CircuitMonkey/eight-bit-computer-m1/modules/alu/m1-alu.brd

## EAGLE design modules/alu/m1-alu.brd (2020-04-13)

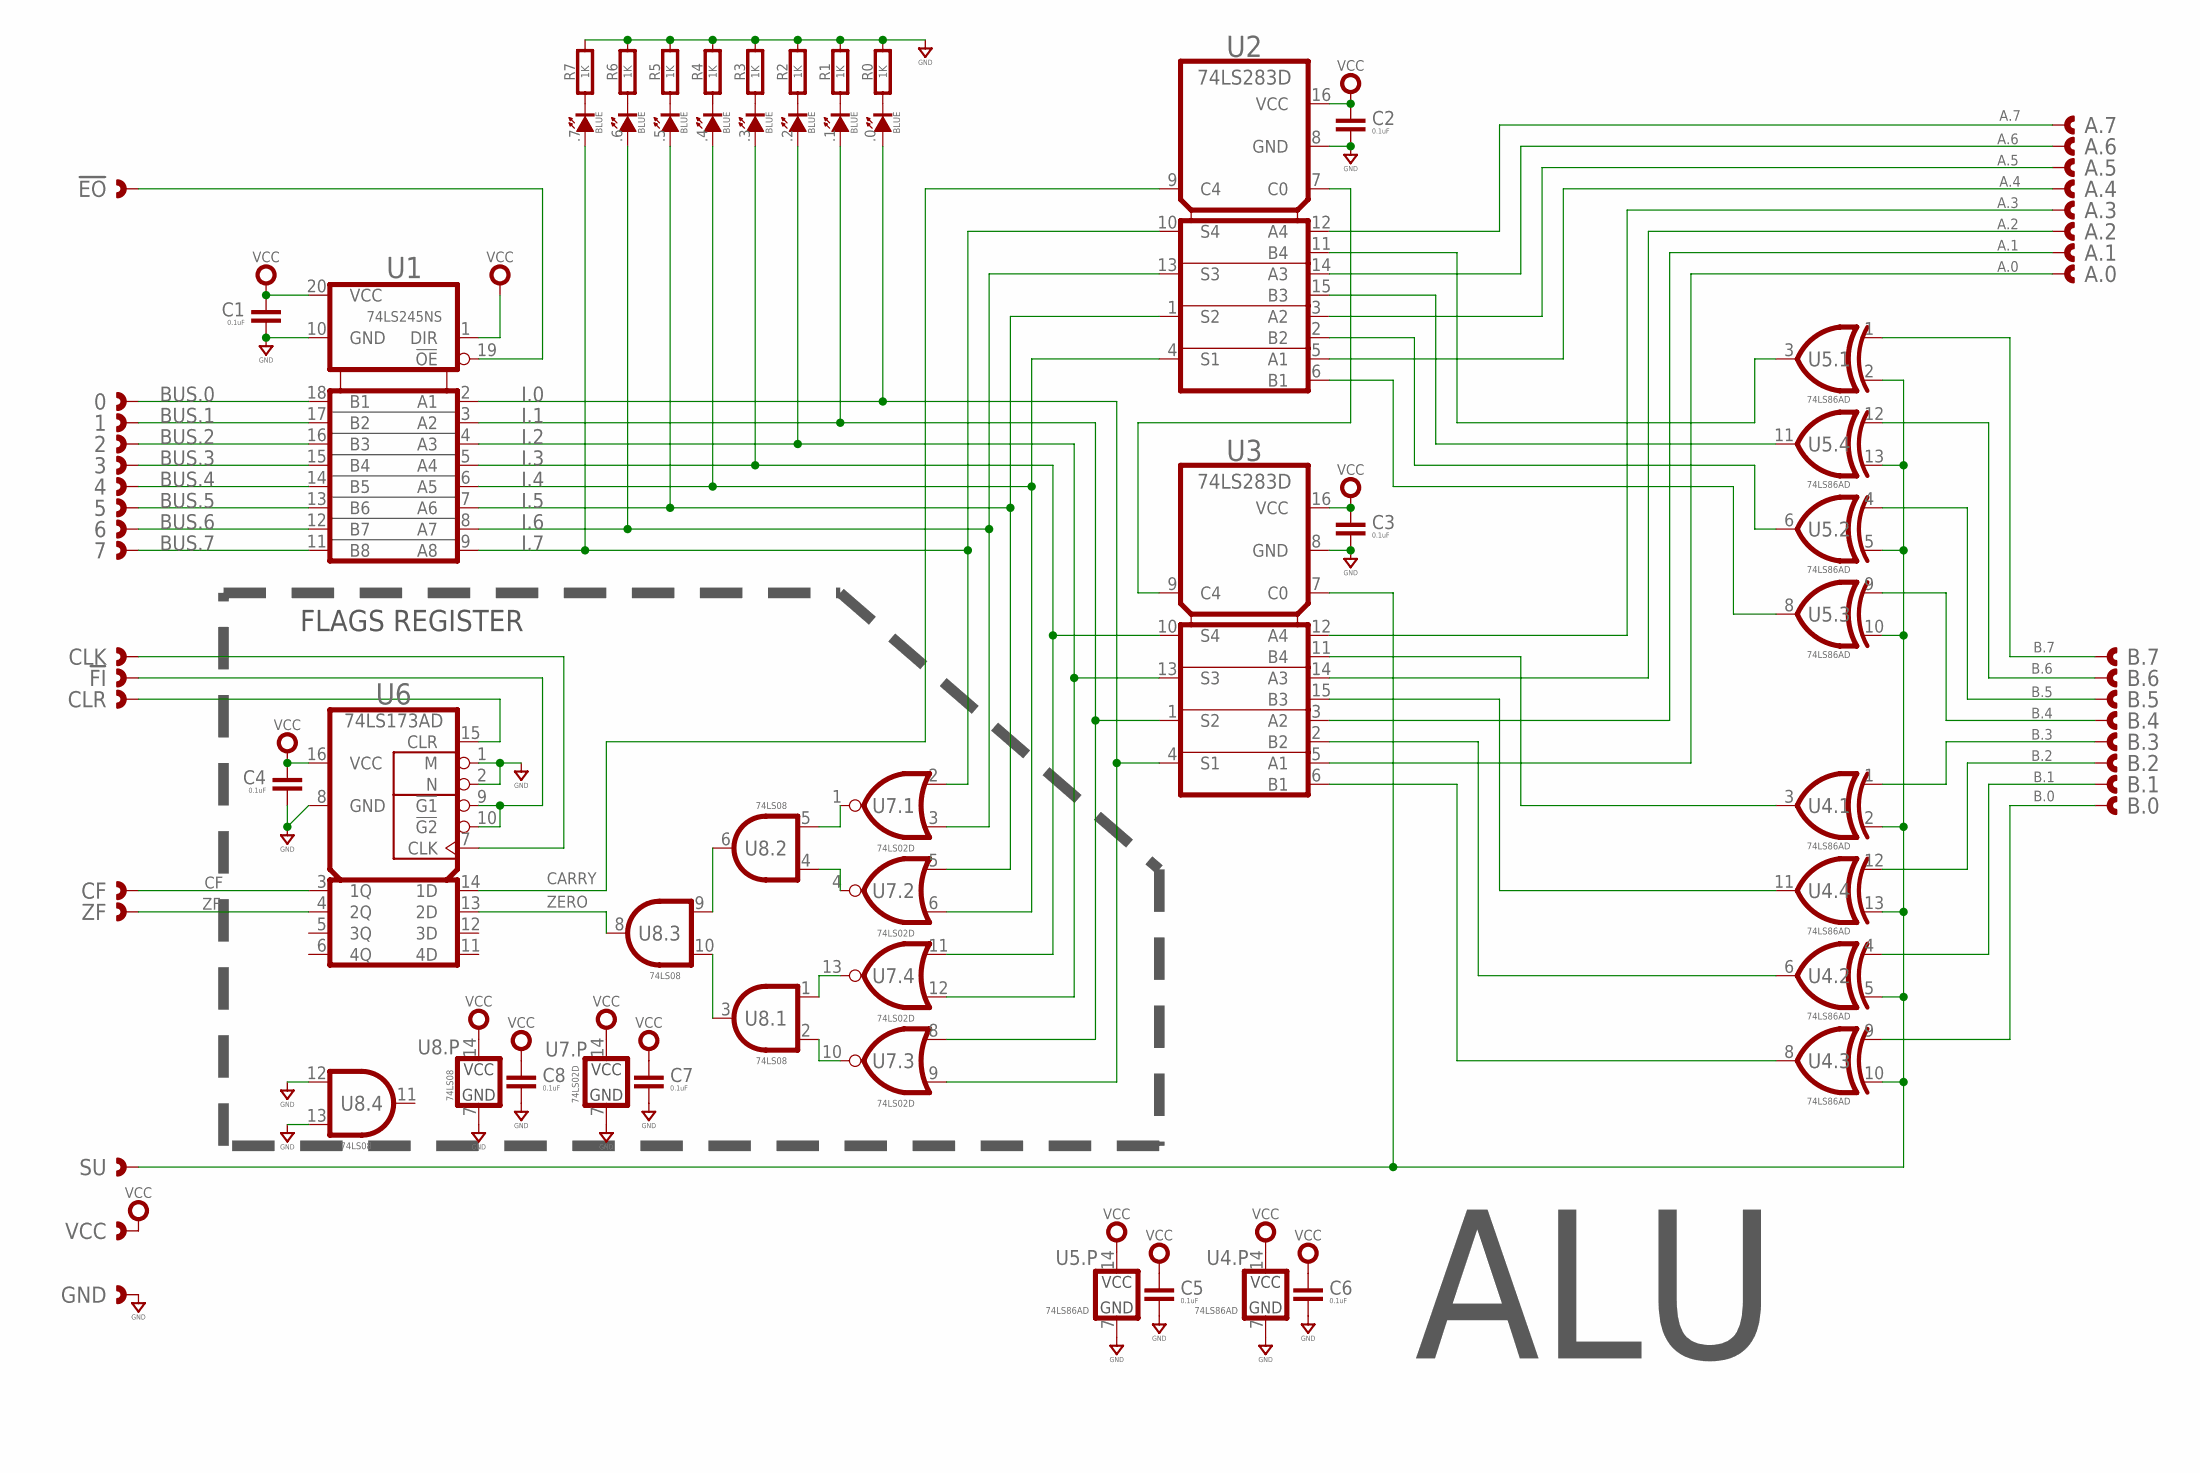
[picture p24: schematic m1-alu.sch]

Parts:
0, 1, 2, 3, 4, 5, 6, 7: CAST-01X1; CAST01-2.54MM
!EO: CAST-01X1; CAST01-2.54MM
!FI: CAST-01X1; CAST01-2.54MM
.0, .1, .2, .3, .4, .5, .6, .7: BLUE; SMD_0603
A.0, A.1, A.2, A.3, A.4, A.5, A.6, A.7: CAST-01X1; CAST01-2.54MM
B.0, B.1, B.2, B.3, B.4, B.5, B.6, B.7: CAST-01X1; CAST01-2.54MM
C1, C2, C3, C4, C5, C6, C7, C8: 0.1uF; 0603-CAP
CF: CAST-01X1; CAST01-2.54MM
CLK: CAST-01X1; CAST01-2.54MM
CLR: CAST-01X1; CAST01-2.54MM
GND: CAST-01X1; CAST01-2.54MM
R0, R1, R2, R3, R4, R5, R6, R7: 1K; 0603-RES
SU: CAST-01X1; CAST01-2.54MM
U1: 74LS245NS; SO20
U2, U3: 74LS283D; SO16
U4, U5: 74LS86AD; SOP14
U6: 74LS173AD; SO16
U7: 74LS02D; SOP14
U8: 74LS08; SOP14
VCC: CAST-01X1; CAST01-2.54MM
ZF: CAST-01X1; CAST01-2.54MM

Connections:
A.0: A.0.1, U3.5 (A1)
A.1: A.1.1, U3.3 (A2)
A.2: A.2.1, U3.14 (A3)
A.3: A.3.1, U3.12 (A4)
A.4: A.4.1, U2.5 (A1)
A.5: A.5.1, U2.3 (A2)
A.6: A.6.1, U2.14 (A3)
A.7: A.7.1, U2.12 (A4)
B.0: B.0.1, U4.9 (A)
B.1: B.1.1, U4.4 (A)
B.2: B.2.1, U4.12 (A)
B.3: B.3.1, U4.1 (A)
B.4: B.4.1, U5.9 (A)
B.5: B.5.1, U5.4 (A)
B.6: B.6.1, U5.12 (A)
B.7: B.7.1, U5.1 (A)
BUS.0: 0.1, U1.18 (B1)
BUS.1: 1.1, U1.17 (B2)
BUS.2: 2.1, U1.16 (B3)
BUS.3: 3.1, U1.15 (B4)
BUS.4: 4.1, U1.14 (B5)
BUS.5: 5.1, U1.13 (B6)
BUS.6: 6.1, U1.12 (B7)
BUS.7: 7.1, U1.11 (B8)
CARRY: U2.9 (C4), U6.14 (1D)
CF: CF.1, U6.3 (1Q)
GND: C1.2, C2.2, C3.2, C4.2, C5.2, C6.2, C7.2, C8.2, GND.1, R0.2, R1.2, R2.2, R3.2, R4.2, R5.2, R6.2, R7.2, U1.10 (GND), U2.8 (GND), U3.8 (GND), U4.7 (GND), U5.7 (GND), U6.1 (M), U6.2 (N), U6.8 (GND), U7.7 (GND), U8.7 (GND), U8.12 (A), U8.13 (B)
I.0: .0.A, U1.2 (A1), U3.4 (S1), U7.9 (B)
I.1: .1.A, U1.3 (A2), U3.1 (S2), U7.8 (A)
I.2: .2.A, U1.4 (A3), U3.13 (S3), U7.12 (B)
I.3: .3.A, U1.5 (A4), U3.10 (S4), U7.11 (A)
I.4: .4.A, U1.6 (A5), U2.4 (S1), U7.6 (B)
I.5: .5.A, U1.7 (A6), U2.1 (S2), U7.5 (A)
I.6: .6.A, U1.8 (A7), U2.13 (S3), U7.3 (B)
I.7: .7.A, U1.9 (A8), U2.10 (S4), U7.2 (A)
unnamed: U2.7 (C0), U3.9 (C4)
unnamed: SU.1, U3.7 (C0), U4.2 (B), U4.5 (B), U4.10 (B), U4.13 (B), U5.2 (B), U5.5 (B), U5.10 (B), U5.13 (B)
unnamed: U2.11 (B4), U5.3 (Y)
unnamed: U2.15 (B3), U5.11 (Y)
unnamed: U2.2 (B2), U5.6 (Y)
unnamed: U2.6 (B1), U5.8 (Y)
unnamed: U3.6 (B1), U4.8 (Y)
unnamed: U3.2 (B2), U4.6 (Y)
unnamed: U3.15 (B3), U4.11 (Y)
unnamed: U3.11 (B4), U4.3 (Y)
unnamed: U7.1 (Y), U8.5 (B)
unnamed: U7.4 (Y), U8.4 (A)
unnamed: U8.6 (Y), U8.9 (A)
unnamed: U8.3 (Y), U8.10 (B)
unnamed: U7.13 (Y), U8.1 (A)
unnamed: U7.10 (Y), U8.2 (B)
unnamed: !EO.1, U1.19 (!OE)
unnamed: .0.K (C), R0.1
unnamed: .1.K (C), R1.1
unnamed: .2.K (C), R2.1
unnamed: .3.K (C), R3.1
unnamed: .4.K (C), R4.1
unnamed: .5.K (C), R5.1
unnamed: .6.K (C), R6.1
unnamed: .7.K (C), R7.1
unnamed: !FI.1, U6.9 (!G1), U6.10 (!G2)
unnamed: CLK.1, U6.7 (CLK)
unnamed: CLR.1, U6.15 (CLR)
VCC: C1.1, C2.1, C3.1, C4.1, C5.1, C6.1, C7.1, C8.1, U1.20 (VCC), U2.16 (VCC), U3.16 (VCC), U4.14 (VCC), U5.14 (VCC), U6.16 (VCC), U7.14 (VCC), U8.14 (VCC), VCC.1
ZERO: U6.13 (2D), U8.8 (Y)
ZF: U6.4 (2Q), ZF.1

Notes on the sheet:
ALU
FLAGS REGISTER

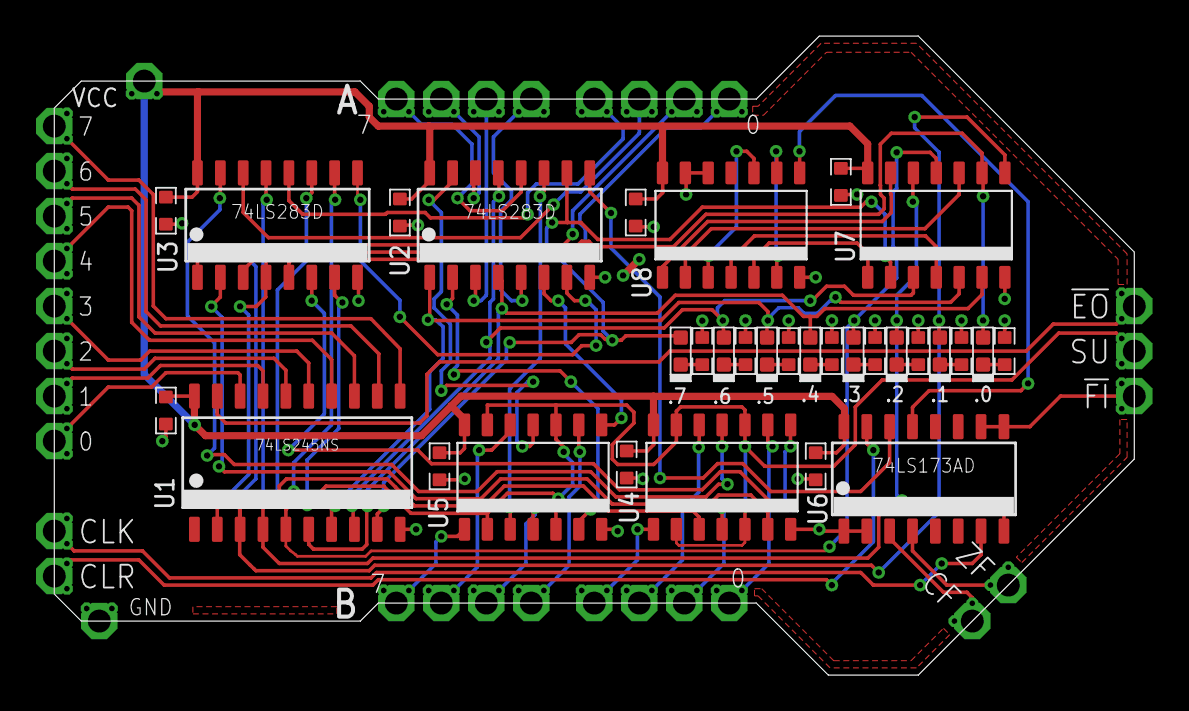
[picture p25: board m1-alu.brd from above]

Board: 2 copper layers, 60.0 x 35.5 mm, 65 parts (0 on the bottom side), 66 nets.
